OmkarTikekar0037/USB_to_Ethernet_ZOHO/images/USB_3.1_to_Ethernet_F.png

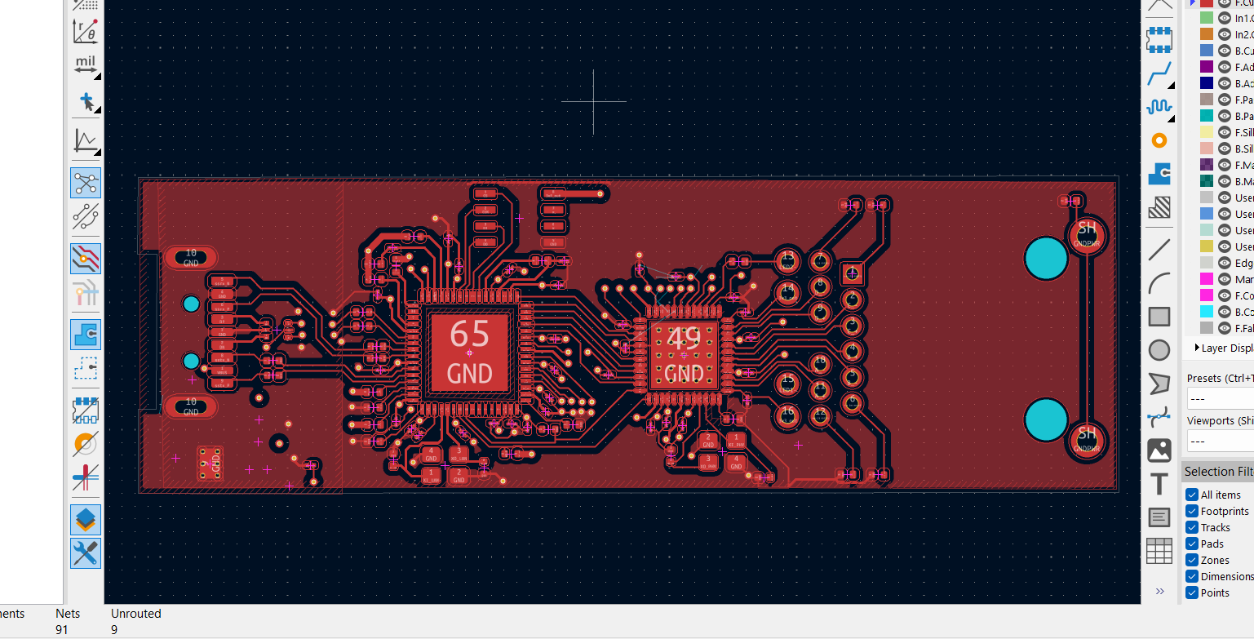
images/USB_3.1_to_Ethernet_F.png
