OmkarTikekar0037/USB_to_Ethernet_ZOHO/images/USB_3.1_to_Ethernet_pwr.png

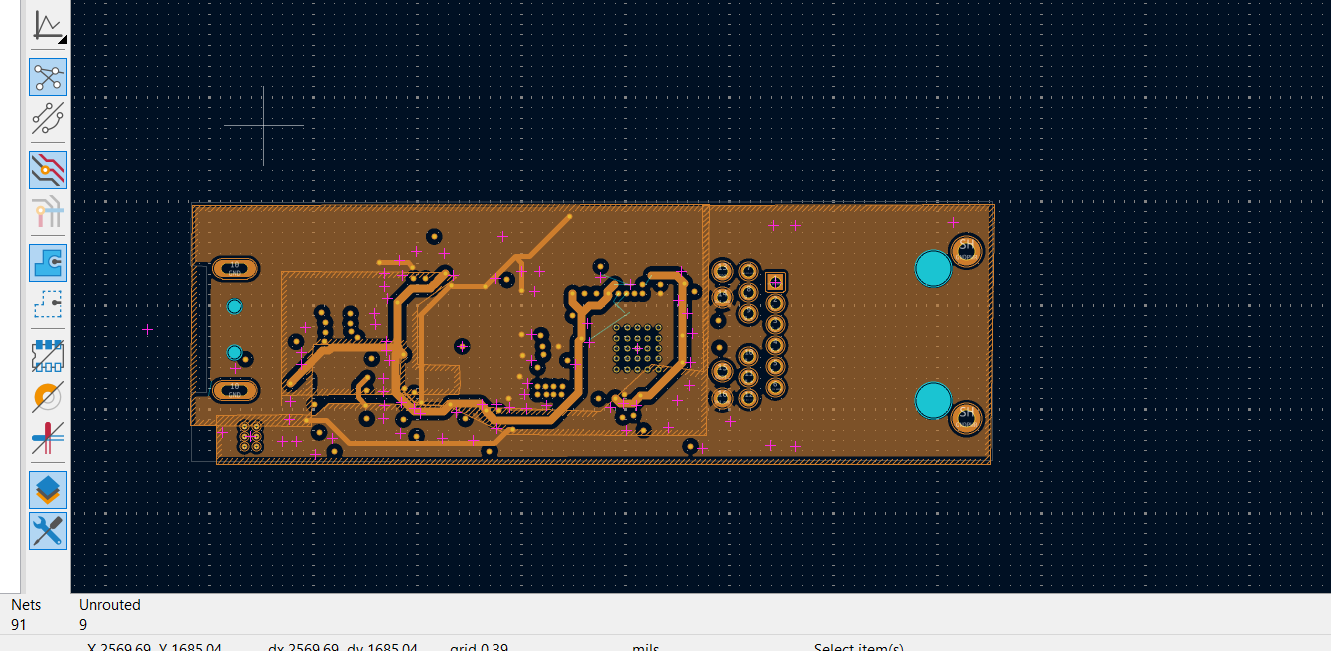
images/USB_3.1_to_Ethernet_pwr.png
